ramkumarkcse/Automated-drip-irrigation-using-rasbery-pi/images/block-scheme.png

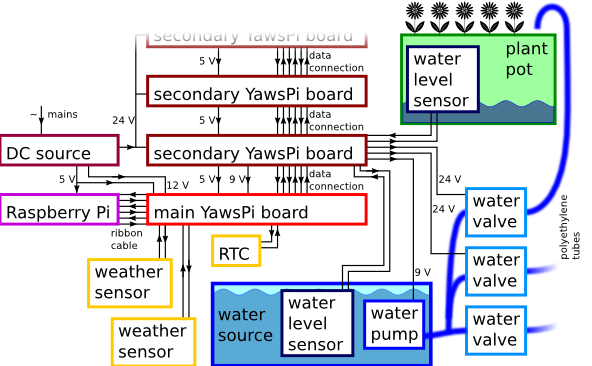
images/block-scheme.png
