ramkumarkcse/Automated-drip-irrigation-using-rasbery-pi/images/humidity_sensor_Keyes_DHT11.jpg

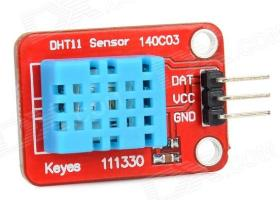
images/humidity_sensor_Keyes_DHT11.jpg
