ramkumarkcse/Automated-drip-irrigation-using-rasbery-pi/images/illuminance_sensor_BH1750FVI.jpg

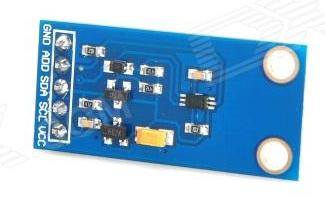
images/illuminance_sensor_BH1750FVI.jpg
