ramkumarkcse/Automated-drip-irrigation-using-rasbery-pi/images/pcb_main_small.jpg

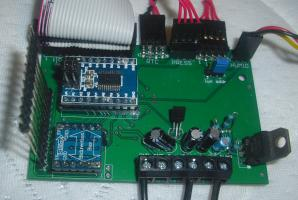
images/pcb_main_small.jpg
