ramkumarkcse/Automated-drip-irrigation-using-rasbery-pi/images/pins_numbering_yawspi-sec.png

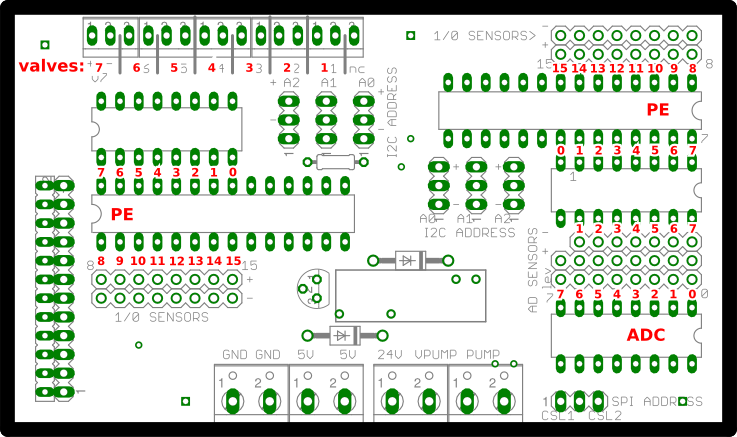
images/pins_numbering_yawspi-sec.png
