ramkumarkcse/Automated-drip-irrigation-using-rasbery-pi/images/power_source_Mean_Well_RQ-85D.jpg

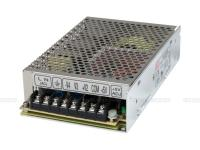
images/power_source_Mean_Well_RQ-85D.jpg
