ramkumarkcse/Automated-drip-irrigation-using-rasbery-pi/images/pressure_sensor_BMP180.jpg

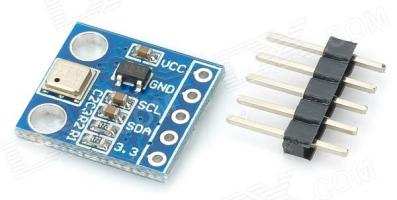
images/pressure_sensor_BMP180.jpg
