ramkumarkcse/Automated-drip-irrigation-using-rasbery-pi/images/RTC.jpg

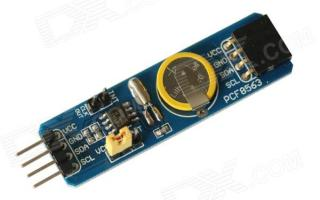
images/RTC.jpg
