ramkumarkcse/Automated-drip-irrigation-using-rasbery-pi/images/tubing_cross.jpg

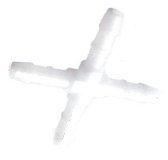
images/tubing_cross.jpg
