ramkumarkcse/Automated-drip-irrigation-using-rasbery-pi/images/tubing_joint.jpg

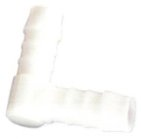
images/tubing_joint.jpg
