ramkumarkcse/Automated-drip-irrigation-using-rasbery-pi/images/valve_tubing.jpg

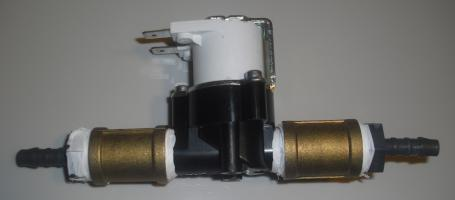
images/valve_tubing.jpg
