ramkumarkcse/Automated-drip-irrigation-using-rasbery-pi/images/voltage_74LVC8T245_conversion_module.jpg

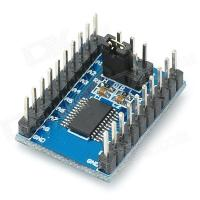
images/voltage_74LVC8T245_conversion_module.jpg
