ramkumarkcse/Automated-drip-irrigation-using-rasbery-pi/images/voltage_JY-MCU_4-way_converter.jpg

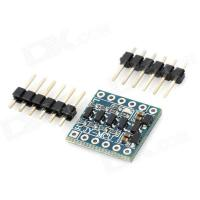
images/voltage_JY-MCU_4-way_converter.jpg
