ramkumarkcse/Automated-drip-irrigation-using-rasbery-pi/images/water_level_sensor_hamlin.png

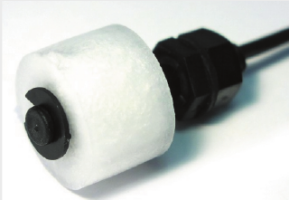
images/water_level_sensor_hamlin.png
