ramkumarkcse/Automated-drip-irrigation-using-rasbery-pi/images/water_valve_VIVA_Sanela_VE-RPE4115NC.jpg

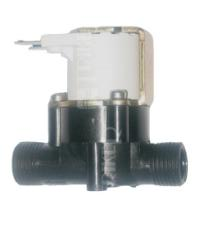
images/water_valve_VIVA_Sanela_VE-RPE4115NC.jpg
