ramkumarkcse/Automated-drip-irrigation-using-rasbery-pi/images/webpage-home-brdr.png

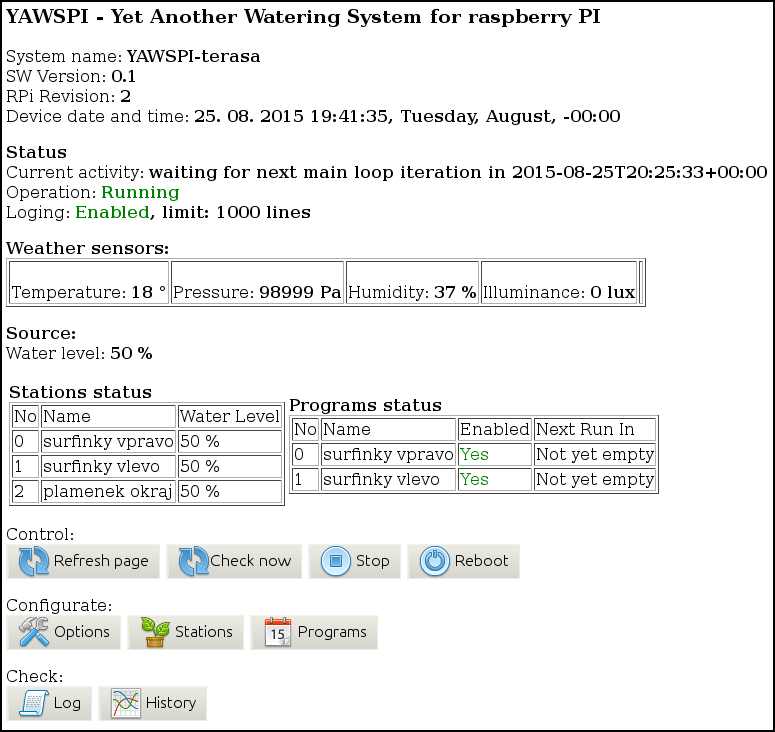
images/webpage-home-brdr.png
