ramkumarkcse/Automated-drip-irrigation-using-rasbery-pi/images/webpage-log-brdr.png

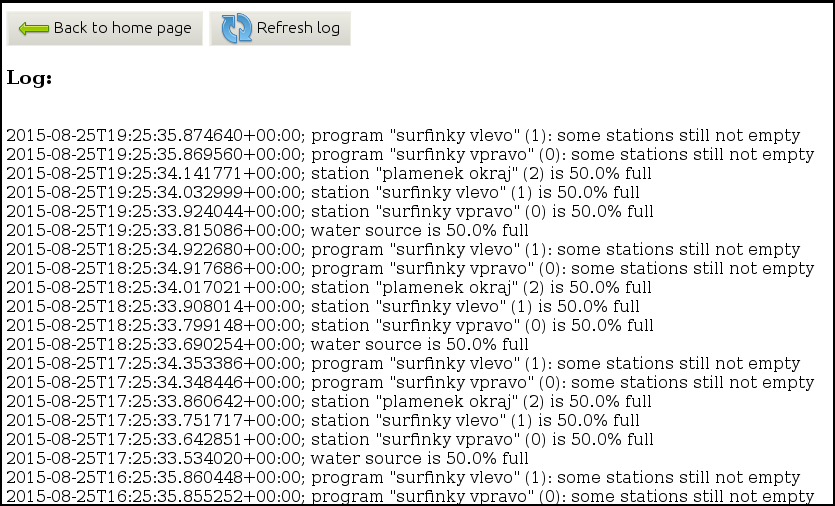
images/webpage-log-brdr.png
