ramkumarkcse/Automated-drip-irrigation-using-rasbery-pi/images/webpage-options-brdr.png

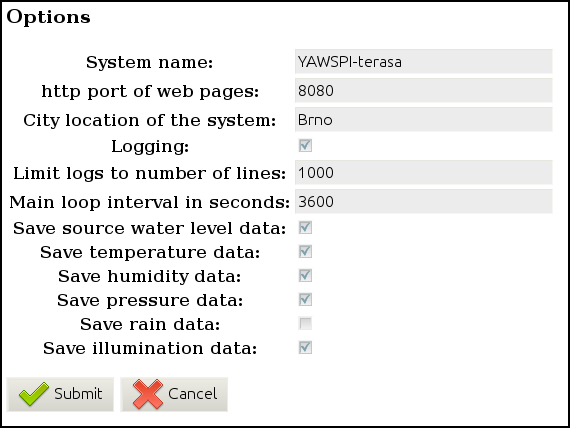
images/webpage-options-brdr.png
