ramkumarkcse/Automated-drip-irrigation-using-rasbery-pi/images/webpage-programs-brdr.png

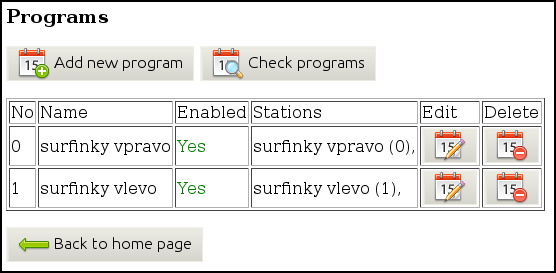
images/webpage-programs-brdr.png
