ramkumarkcse/Automated-drip-irrigation-using-rasbery-pi/images/webpage-stations-brdr.png

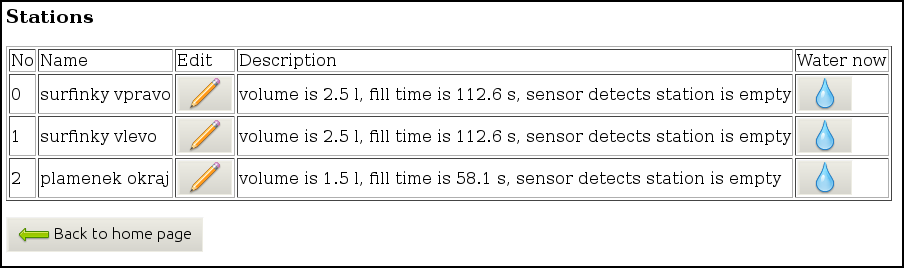
images/webpage-stations-brdr.png
