ramkumarkcse/Automated-drip-irrigation-using-rasbery-pi/images/webpage-stations-settings-brdr.png

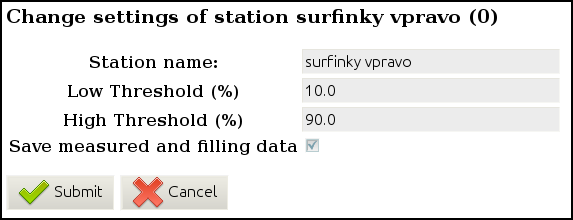
images/webpage-stations-settings-brdr.png
