ramkumarkcse/Automated-drip-irrigation-using-rasbery-pi/images/operation-scheme-all.png

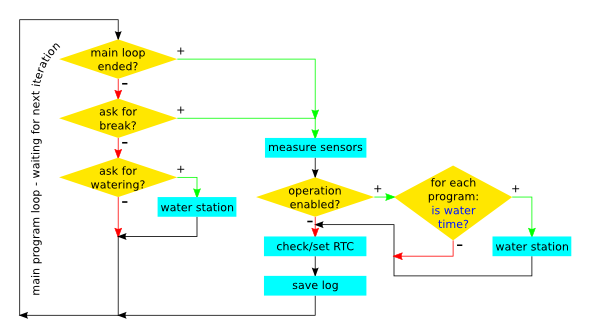
images/operation-scheme-all.png
