ramkumarkcse/Automated-drip-irrigation-using-rasbery-pi/images/operation-scheme-iswatertime.png

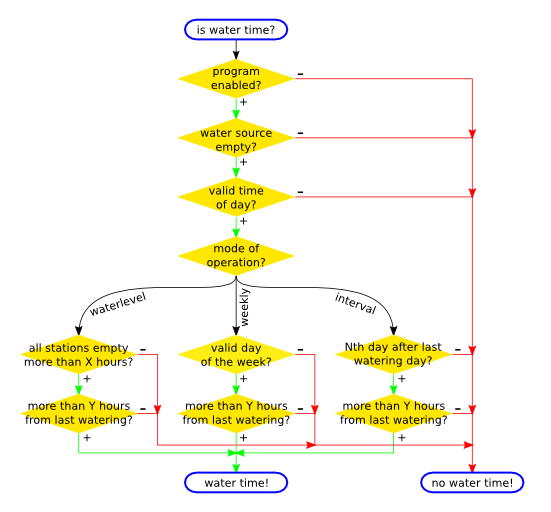
images/operation-scheme-iswatertime.png
