ramkumarkcse/Automated-drip-irrigation-using-rasbery-pi/images/webpage-history-brdr.png

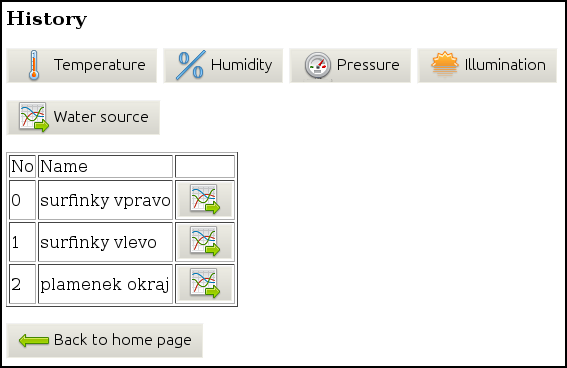
images/webpage-history-brdr.png
