ramkumarkcse/Automated-drip-irrigation-using-rasbery-pi/images/webpage-history-chart-brdr.png

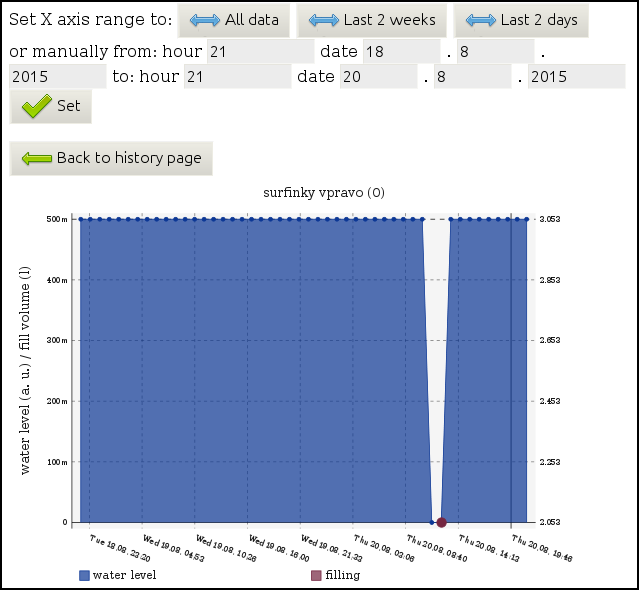
images/webpage-history-chart-brdr.png
