ramkumarkcse/Automated-drip-irrigation-using-rasbery-pi/yawspisw/hw_config.py

#XXX vsude - water station, container to water pot!
#=================================================================
# yawspi hardware configuration
#=================================================================

# hw adress is composed of two numbers - first one is index of the hw device,
# second one is pin number.
# GPIO: [0, X]
# PE1:  [1, X]
# PE2:  [2, X]
# ADC1: [-1, X]
# ADC2: [-2, X]


def hw_config():

    # initialize dictionary with hardware settings:
    tmp = {}
    # ------------------- RTC:
    # is Real Time Clock installed?
    tmp['RTC'] = 1
    #tmp['RTC'] = 0

    # ------------------- IO outputs:
    # expanders MCP23017 (multiple port expanders possible)
    # this must be tuple!, if only one item, add comma after it: (xx,)
    tmp['PeAddresses'] = (0x20, 0x21)

    # ------------------- Analog to Digital Converter:
    # Pins on Raspberry Pi GPIO of the clockpin, misopin, mosipin, cspin for AD
    # converters MCP3008:
    tmp['AdcPins'] = ((23, 19, 21, 13), (23, 19, 21, 24))
    # !!! VRATIT na predchozi radek
    tmp['AdcPins'] = ((23, 19, 21, 24),)
    #tmp['AdcPins'] = ()

    # ------------------- Weather Sensors:
    tmp['SeTemp'] = 1     # temperature sensor present
    # temperature value take from:
    #       'humid': DHT11 (humidity sensor)
    #       'press': BMP180 (pressure sensor)
    tmp['SeTempSource'] = 'press'
    tmp['SeRain'] = 0     # rain sensor present
    tmp['SeRainPin'] = (-2, 1)  # rain sensor pin
    tmp['SeHumid'] = 1    # humidity sensor present
    tmp['SeHumidPin'] = (0, 13)  # humidity sensor present
    tmp['SePress'] = 1    # pressure sensor present
    tmp['SeIllum'] = 1    # illuminance sensor present
    tmp['SeIllumAddrToHigh'] = 0    # illuminance address pin set to high?

    # ------------------- Water Source:
    # source of water with pump (or valve)
    # source capacity: if unlimited, water capacity of the source is -1, else
    # water capacity is limited and volume is in liters
    # pin of pump relay or valve connected to port expander
    # Speed is speed of pump or flow rate of the source approx. flowrate of the
    # pump in litres per second, volume of pumped water is calculated according
    # equation: volume = offset + rate1 * time
    # equation: volume = offset + rate1 * time + rate2 * time^2
    # (offset, rate1)
    # (offset, rate1, rate2)
    # SettleT is time source needs to stop the water flow after switching off
    # 'FlowRate': (0.047501, 0.027133),
    # 'FlowRateRev': (-1.7126, 36.7918),
    # 'FLowRate': (6.0297e-03, 3.2421e-02, -1.2655e-04),
    # 'FlowRateRev': (0.061503, 29.188514, 6.336059),
    tmp['So'] = {
        'Cap': 50,
        'Pin': (1, 0),
        'FlowRate': (6.0297e-03, 3.2421e-02, -1.2655e-04),
        'FlowRateRev': (0.061503, 29.188514, 6.336059),
        'SettleT': 0.1,
    }

    # ------------------- Stations:
    # each station has one valve.
    # Cap is water capacity of each station in litres:
    # Pin is IO pin of valve
    # SettleT is time valve needs to fully open
    tmp['St'] = (
        {
            'Cap': 0.5,
            'Pin': (1, 1),
            'SettleT': 0.1,
        },
        #{
        #    'Cap': 1.0,
        #    'Pin': (1, 2),
        #    'SettleT': 0.1,
        #},
        #{
        #    'Cap':  0.5,
        #    'Pin': (1, 3),
        #    'SettleT': 0.1,
        #},
        #{
        #    'Cap':  0.5,
        #    'Pin': (1, 4),
        #    'SettleT': 0.1,
        #},
        #{
        #    'Cap':  0.5,
        #    'Pin': (1, 5),
        #    'SettleT': 0.1,
        #},
        #{
        #    'Cap':  0.5,
        #    'Pin': (1, 6),
        #    'SettleT': 0.1,
        #},
        #{
        #    'Cap':  0.5,
        #    'Pin': (1, 7),
        #    'SettleT': 0.1,
        #},
    )

    # ------------------- Water Level Sensors:
    # possible sensor types:
    #   none - no water level sensor, amount of water is determined by water
    #       capacity
    #   min - switch at the bottom of the water container of the station
    #       (detects container is empty)
    #   max- switch at the top the water container of the station
    #      (detects container is full)
    #   minmax - switch at the bottom and top of the station water container
    #      (detects container is empty and is full)
    #   grad - some analog sensor
    #
    # last sensor is water source sensor (if source is unlimited, set sensor
    # type none.
    tmp['SeWL'] = (
        #{
        #    'Type':  'none',
        #},
        #{
        #    'Type':  'max',
        #    'Pin':  (1, 8),
        #},
        #{
        #    'Type':  'none',
        #},
        {
            'Type':  'min',
            'Pin':  (1, 10),
        },
        #{
        #    'Type':  'minmax',
        #    'MinPin':  (1, 8),
        #    'MaxPin':  (1, 9),
        #},
        {
            'Type':  'minmax',
            'MinPin':  (1, 9),
            'MaxPin':  (1, 8),
        },
        #{
        #    'Type':  'max',
        #    'Pin':  (1, 15),
        #},
        #{
        #    'Type':  'grad',
        #    'ValuePin':  (-1, 6),
        #    'OnOffPin':  (2, 1),
        #},
        #{
        #    'Type':  'grad',
        #    'ValuePin':  (-2, 0),
        #    'OnOffPin':  (2, 8),
        #},
        #{
        #    'Type':  'none',
        #},
    )

    return tmp
